smorgo/VentController/NodeMCU Code - Not Used/mpl3115a2.lua

-- Library for working with MPL3115A2 I2C Barometric/Altitude sensor
-- As used on breakout board by Adafruit
-- Adapted from code by gareth@l0l.org.uk, Hamish Cunningham and Aeprox@github
-- This code is GPL v3 by steve@wormpurple.com
-- blah blah blah standard licence conditions apply blah blah blah

local moduleName = "mpl3115a2"

local M = {
    MPL3115A2_ADDR            		= 0x60
}
_G[moduleName] = M

local busid = 0 -- i2c bus id

local function read_reg(dev_addr, reg_addr)
     i2c.start(id)
     a = i2c.address(id, dev_addr ,i2c.TRANSMITTER)
	 if a ~= true then 
		print("Device NOT connected")
	end
     i2c.write(id,reg_addr)
     -- i2c.stop(id) < Don't send a stop for this device
     i2c.start(id)
     a = i2c.address(id, dev_addr,i2c.RECEIVER)
	 if a ~= true then 
		print("Device NOT connected")
	end
     c=i2c.read(id,1)
     i2c.stop(id)
     return string.byte(c)
end

local function write_reg(dev_addr, reg_addr, val)
    i2c.start(id)
    a = i2c.address(id, dev_addr ,i2c.TRANSMITTER)
	if a ~= true then 
		print("Device NOT connected")
	end
     c = i2c.write(id,reg_addr, val)
     i2c.stop(id)
end

local function getData(addr) -- Do the actual reading from the sensor
    i2c.setup(id,sda,scl,i2c.SLOW)
	 
	write_reg(addr,0x26,0x38)
	write_reg(addr,0x13,0x07)
	write_reg(addr,0x26,0x39)

	uart.write(0,"Waiting for data from MPL3115A2")
	repeat
		status = read_reg(addr,0x00)
		uart.write(0,".")
	until bit.band(status,0x08) == 0x08 

	print()
	
	local Pmsb = read_reg(addr,0x01)
	local Pcsb = read_reg(addr,0x02)
	local Plsb = read_reg(addr,0x03)
	local Tmsb = read_reg(addr,0x04)
	local Tlsb = read_reg(addr,0x05)

	local p = bit.lshift(Pmsb,8)
	p = bit.bor(p, Pcsb)
	p = bit.lshift(p,8)
	p = bit.bor(p, Plsb)
	p = bit.rshift(p,4)

	local baro = p/4
	 
	local t = (Tmsb * 256) + Tlsb
	t = bit.rshift(t,4)
	t = t/16.0

	return baro, t
end

function M.read()
	i2c.setup(busid, sda , scl, i2c.SLOW)
	baro,temp = getData(M.MPL3115A2_ADDR)
	return baro,temp
end

return M
